MikaPetteriLundgren/Arduino-Domoticz-Gateway/domoticzGatewaySettings.h

/*
  domoticzGatewaySettings.h header file includes settings for the Arduino-Domoticz-Gateway sketch.
  Header file needs to be stored within a same folder with the sketch.
*/
#ifndef domoticzGatewaySettings_h
  #define domoticzGatewaySettings_h

  #define TEMPSENSORIDX 530 // Change correct IDX number here
  #define MQTT_SERVER "192.168.1.93" // IP address of the MQTT server
  #define DEVICE_ID "Uno"

#endif
